GirishTabaraddi/ESP32-Ethernet-Gateway-KiCAD/ESP32_Ethernet_Gateway/power.kicad_sch

## KiCad design ESP32_Ethernet_Gateway/power.kicad_sch (2026-04-19)

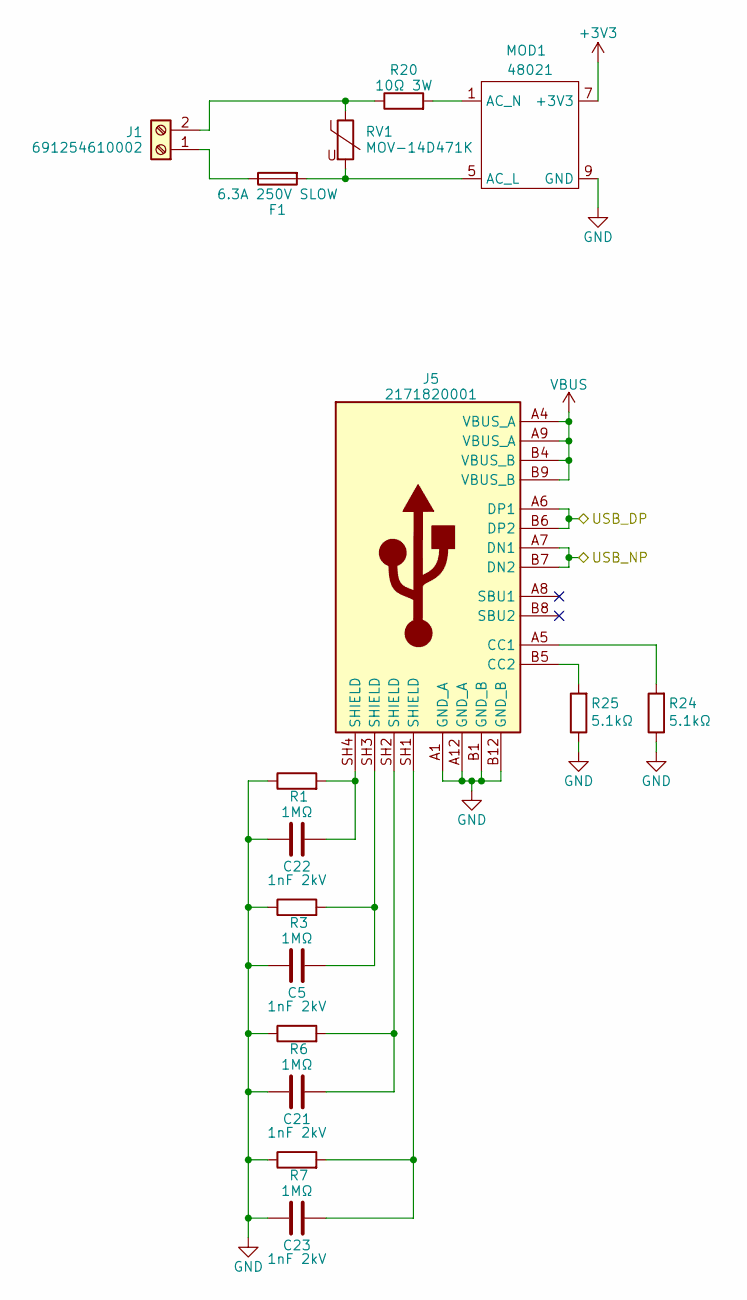
[picture p11: schematic power.kicad_sch]

Parts:
C5, C21, C22, C23: 1nF 2kV; C_1206_3216Metric; Manufacturer Part No Any; JLCPCB Part # C9196
F1: 6.3A 250V SLOW; 3403.0174.11; Manufacturer Part No 3403.0174.11; JLCPCB Part # C3157803
J1: 691254610002; Manufacturer Part No 691254610002; JLCPCB Part # C6080850
J5: 2171820001; Manufacturer Part No 2171820001; JLCPCB Part # C3197815
MOD1: 48021; Manufacturer Part No 48021
R1, R3, R6, R7: 1MΩ; R_0603_1608Metric; Manufacturer Part No Any; JLCPCB Part # C22935
R20: 10Ω 3W; EP3WS10RJ; Manufacturer Part No EP3WS10RJ; JLCPCB Part # C1366424
R24, R25: 5.1kΩ; R_0603_1608Metric; Manufacturer Part No Any; JLCPCB Part # C23186
RV1: MOV-14D471K; MOV14D471K; Manufacturer Part No MOV-14D471K; JLCPCB Part # C1527439

Connections:
+3V3: MOD1.7 (+3V3)
GND: C5.1, C21.1, C22.1, C23.1, J5.A1 (GND_A), J5.A12 (GND_A), J5.B1 (GND_B), J5.B12 (GND_B), MOD1.9 (GND), R1.1, R3.1, R6.1, R7.1, R24.1, R25.1
unnamed: C5.2, J5.SH3 (SHIELD), R3.2
unnamed: C21.2, J5.SH2 (SHIELD), R6.2
unnamed: C22.2, J5.SH4 (SHIELD), R1.2
unnamed: C23.2, J5.SH1 (SHIELD), R7.2
unnamed: F1.1, J1.1
unnamed: F1.2, MOD1.5 (AC_L), RV1.2
unnamed: J1.2, R20.1, RV1.1
unnamed: J5.A5 (CC1), R24.2
unnamed: J5.B5 (CC2), R25.2
unnamed: MOD1.1 (AC_N), R20.2
USB_DP: J5.A6 (DP1), J5.B6 (DP2)
USB_NP: J5.A7 (DN1), J5.B7 (DN2)
VBUS: J5.A4 (VBUS_A), J5.A9 (VBUS_A), J5.B4 (VBUS_B), J5.B9 (VBUS_B)
