GirishTabaraddi/ESP32-Ethernet-Gateway-KiCAD/ESP32_Ethernet_Gateway/som.kicad_sch

## KiCad design ESP32_Ethernet_Gateway/som.kicad_sch (2026-04-19)

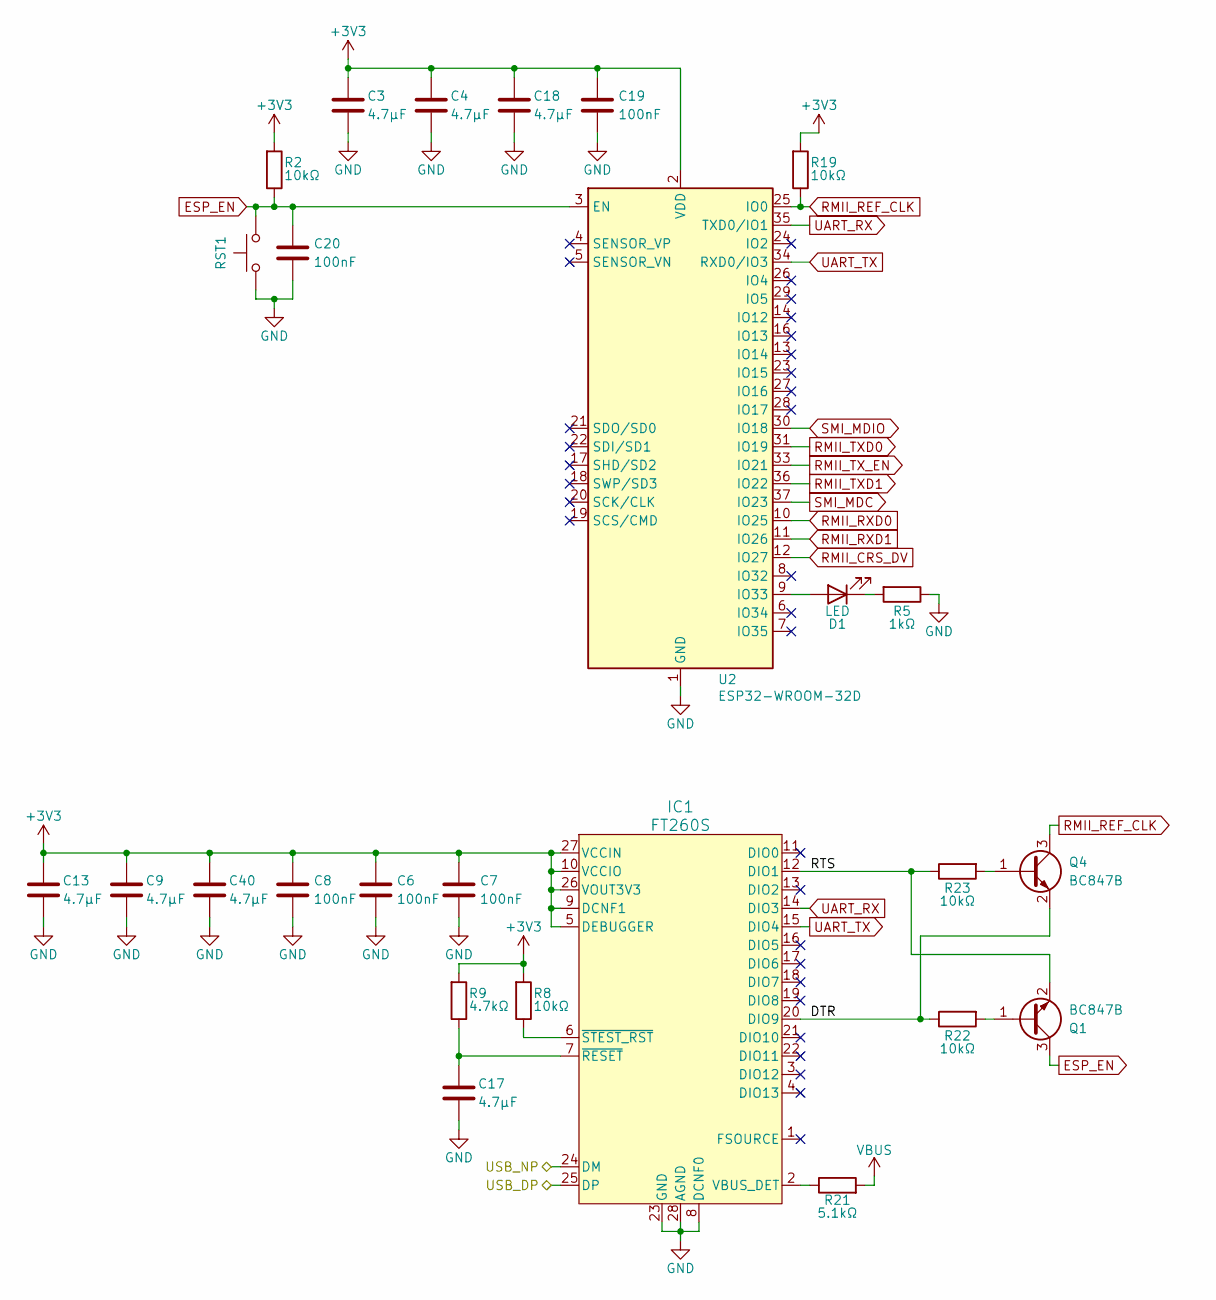
[picture p12: schematic som.kicad_sch]

Parts:
C3, C4, C9, C13, C17, C18, C40: 4.7µF; C_0805_2012Metric; Manufacturer Part No Any; JLCPCB Part # C354262
C6, C7, C8, C19, C20: 100nF; C_0603_1608Metric; Manufacturer Part No Any; JLCPCB Part # C14663
D1: LED; LED_0603_1608Metric; Manufacturer Part No KT-0603R; JLCPCB Part # C2286
IC1: FT260S; TSSOP28_FT260S_FTD; Manufacturer Part No FT260S-x; JLCPCB Part # C85692
Q1, Q4: BC847B; SOT-23; Manufacturer Part No BC847B,215; JLCPCB Part # C2146
R2, R8, R19, R22, R23: 10kΩ; R_0603_1608Metric; Manufacturer Part No Any; JLCPCB Part # C25804
R5: 1kΩ; R_0603_1608Metric; Manufacturer Part No Any; JLCPCB Part # C21190
R9: 4.7kΩ; R_0603_1608Metric; Manufacturer Part No Any; JLCPCB Part # C23162
R21: 5.1kΩ; R_0603_1608Metric; Manufacturer Part No Any; JLCPCB Part # C23186
RST1: RST1; SW_Push_1P1T_NO_CK_KMR2; Manufacturer Part No KMR223NGULCLFG; JLCPCB Part # C2804637
U2: ESP32-WROOM-32D; Manufacturer Part No ESP32-WROOM-32D-N4; JLCPCB Part # C473012

Connections:
+3V3: C3.1, C4.1, C6.1, C7.1, C8.1, C9.1, C13.1, C18.1, C19.1, C40.1, IC1.5 (DEBUGGER), IC1.9 (DCNF1), IC1.10 (VCCIO), IC1.26 (VOUT3V3), IC1.27 (VCCIN), R2.2, R8.2, R9.2, R19.2, U2.2 (VDD)
DTR: IC1.20 (DIO9), Q4.2 (E), R22.1
ESP_EN: C20.1, Q1.3 (C), R2.1, RST1.2, U2.3 (EN)
GND: C3.2, C4.2, C6.2, C7.2, C8.2, C9.2, C13.2, C17.2, C18.2, C19.2, C20.2, C40.2, IC1.8 (DCNF0), IC1.23 (GND), IC1.28 (AGND), R5.1, RST1.1, U2.1 (GND), U2.15 (GND), U2.38 (GND), U2.39 (GND)
unnamed: C17.1, IC1.7 (~RESET), R9.1
unnamed: D1.1 (K), R5.2
unnamed: D1.2 (A), U2.9 (IO33)
unnamed: IC1.2 (VBUS_DET), R21.1
unnamed: IC1.6 (~STEST_RST), R8.1
unnamed: Q1.1 (B), R22.2
unnamed: Q4.1 (B), R23.2
RMII_CRS_DV: U2.12 (IO27)
RMII_REF_CLK: Q4.3 (C), R19.1, U2.25 (IO0)
RMII_RXD0: U2.10 (IO25)
RMII_RXD1: U2.11 (IO26)
RMII_TXD0: U2.31 (IO19)
RMII_TXD1: U2.36 (IO22)
RMII_TX_EN: U2.33 (IO21)
RTS: IC1.12 (DIO1), Q1.2 (E), R23.1
SMI_MDC: U2.37 (IO23)
SMI_MDIO: U2.30 (IO18)
UART_RX: IC1.14 (DIO3), U2.35 (TXD0/IO1)
UART_TX: IC1.15 (DIO4), U2.34 (RXD0/IO3)
USB_DP: IC1.25 (DP)
USB_NP: IC1.24 (DM)
VBUS: R21.2
