GirishTabaraddi/ESP32-Ethernet-Gateway-KiCAD/ESP32_Ethernet_Gateway/switch.kicad_sch

## KiCad design ESP32_Ethernet_Gateway/switch.kicad_sch (2026-04-19)

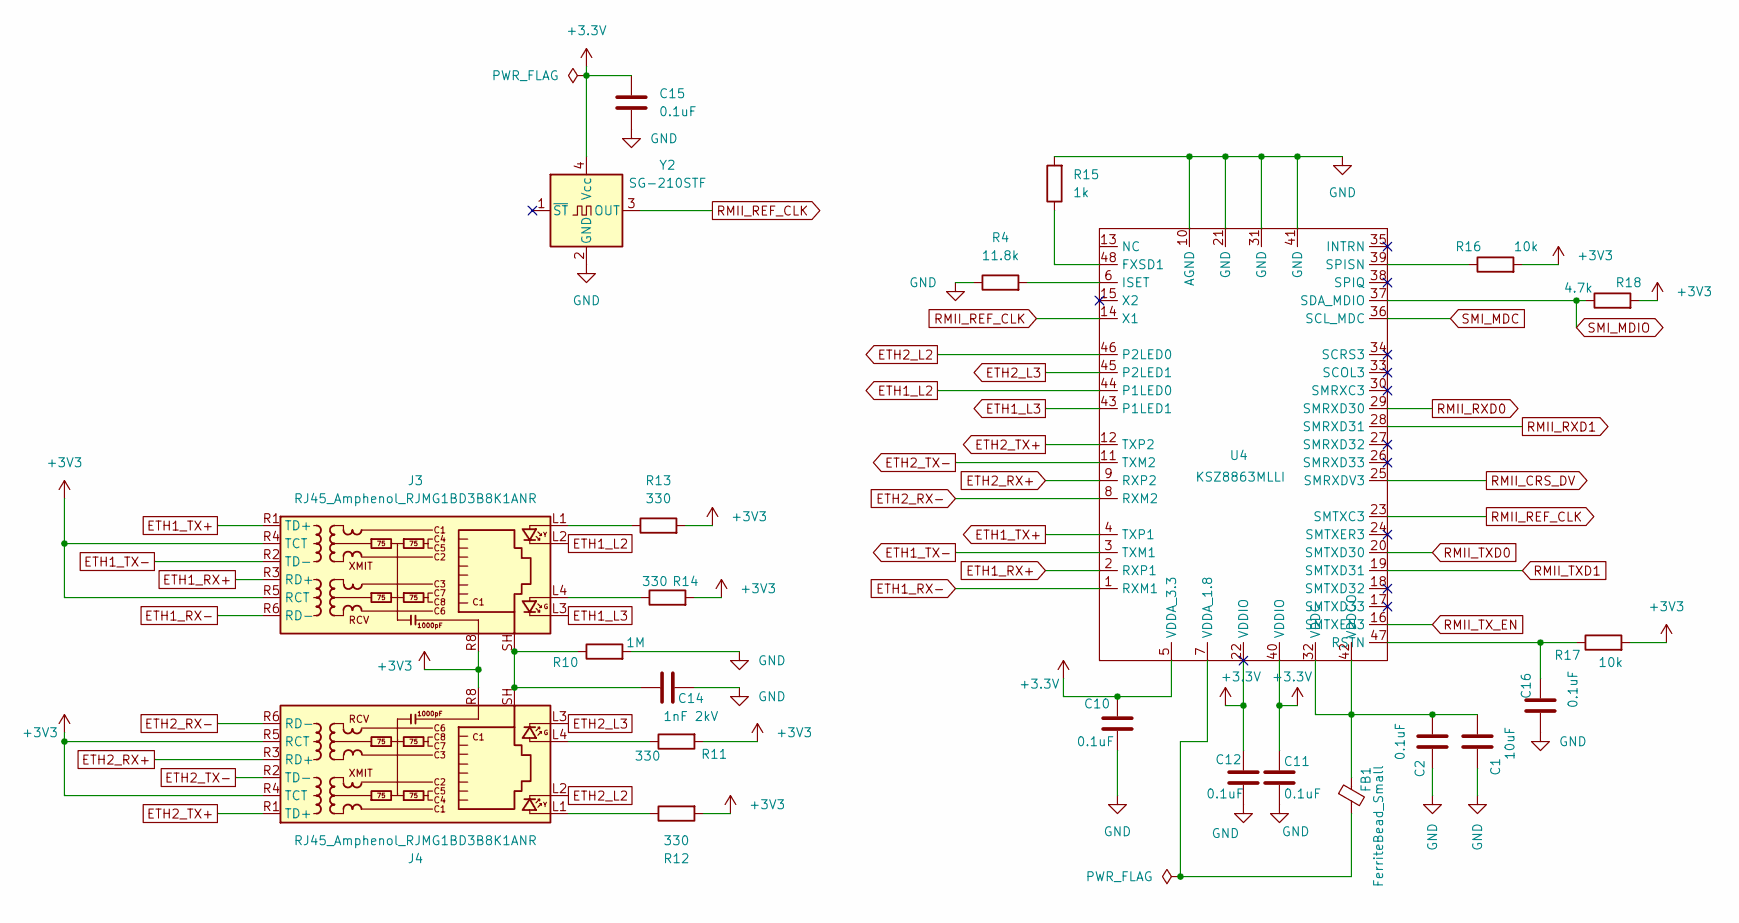
[picture p13: schematic switch.kicad_sch]

Parts:
C1: 10uF; C_0805_2012Metric; Manufacturer Part No GRM21BR71A106KA73L; JLCPCB Part # C117956
C2, C10, C11, C12, C15, C16: 0.1uF; C_0805_2012Metric; Manufacturer Part No CC0805KRX7R9BB104; JLCPCB Part # C49678
C14: 1nF 2kV; C_1812_4532Metric; Manufacturer Part No GR443QR73D102KW01L; JLCPCB Part # C161357
FB1: FerriteBead_Small; L_0805_2012Metric; Manufacturer Part No BLM21PG600SN1D; JLCPCB Part # C18305
J3, J4: RJ45_Amphenol_RJMG1BD3B8K1ANR; Manufacturer Part No RJMG1BD3B8K1ANR; JLCPCB Part # C5119251
R4: 11.8k; R_0805_2012Metric; Manufacturer Part No RC0805FR-0711K8L; JLCPCB Part # C273993
R10: 1M; R_0805_2012Metric; Manufacturer Part No RC0805FR-071ML; JLCPCB Part # C107700
R11, R12, R13, R14: 330; R_0805_2012Metric; Manufacturer Part No RC0805FR-07330RL; JLCPCB Part # C105878
R15: 1k; R_0805_2012Metric; Manufacturer Part No RC0805FR-071KL; JLCPCB Part # C95781
R16, R17: 10k; R_0805_2012Metric; Manufacturer Part No RC0805FR-0710KL; JLCPCB Part # C84376
R18: 4.7k; R_0805_2012Metric; Manufacturer Part No RC0805FR-074K7L; JLCPCB Part # C60816
U4: KSZ8863MLLI; KSZ8863MLLI_LQFP-48_7x7mm_P0.5mm; Manufacturer Part No KSZ8863MLLI; JLCPCB Part # C219151
Y2: SG-210STF; Oscillator_SMD_SeikoEpson_SG210-4Pin_2.5x2.0mm; Manufacturer Part No SG-210STF 50.0000ML5; JLCPCB Part # C17669095

Connections:
+3.3V: C10.2, C11.1, C12.1, C15.2, U4.5 (VDDA_3.3), U4.22 (VDDIO), U4.40 (VDDIO), Y2.4 (Vcc)
+3V3: J3.R4 (TCT), J3.R5 (RCT), J3.R8, J4.R4 (TCT), J4.R5 (RCT), J4.R8, R11.2, R12.2, R13.2, R14.2, R16.2, R17.2, R18.2
ETH1_L2: J3.L2, U4.44 (P1LED0)
ETH1_L3: J3.L3, U4.43 (P1LED1)
ETH1_RX+: J3.R3 (RD+), U4.2 (RXP1)
ETH1_RX-: J3.R6 (RD-), U4.1 (RXM1)
ETH1_TX+: J3.R1 (TD+), U4.4 (TXP1)
ETH1_TX-: J3.R2 (TD-), U4.3 (TXM1)
ETH2_L2: J4.L2, U4.46 (P2LED0)
ETH2_L3: J4.L3, U4.45 (P2LED1)
ETH2_RX+: J4.R3 (RD+), U4.9 (RXP2)
ETH2_RX-: J4.R6 (RD-), U4.8 (RXM2)
ETH2_TX+: J4.R1 (TD+), U4.12 (TXP2)
ETH2_TX-: J4.R2 (TD-), U4.11 (TXM2)
GND: C1.2, C2.2, C10.1, C11.2, C12.2, C14.2, C15.1, C16.1, R4.1, R10.2, R15.2, U4.10 (AGND), U4.21 (GND), U4.31 (GND), U4.41 (GND), Y2.2 (GND)
unnamed: C1.1, C2.1, FB1.1, U4.32 (VDDC), U4.42 (VDDCO)
unnamed: C14.1, J3.SH, J4.SH, R10.1
unnamed: C16.2, R17.1, U4.47 (RSTN)
unnamed: FB1.2, U4.7 (VDDA_1.8)
unnamed: J3.L1, R13.1
unnamed: J3.L4, R14.1
unnamed: J4.L1, R12.1
unnamed: J4.L4, R11.1
unnamed: R4.2, U4.6 (ISET)
unnamed: R15.1, U4.48 (FXSD1)
unnamed: R16.1, U4.39 (SPISN)
RMII_CRS_DV: U4.25 (SMRXDV3)
RMII_REF_CLK: U4.14 (X1), U4.23 (SMTXC3), Y2.3 (OUT)
RMII_RXD0: U4.29 (SMRXD30)
RMII_RXD1: U4.28 (SMRXD31)
RMII_TXD0: U4.20 (SMTXD30)
RMII_TXD1: U4.19 (SMTXD31)
RMII_TX_EN: U4.16 (SMTXEN3)
SMI_MDC: U4.36 (SCL_MDC)
SMI_MDIO: R18.1, U4.37 (SDA_MDIO)
